Laboratorio-de-audio-del-CMM/IxTL-074/Esquemático/IxTL-074_v.1.0.0.kicad_sch

## KiCad design Esquemático/IxTL-074_v.1.0.0.kicad_sch (2026-10-05)

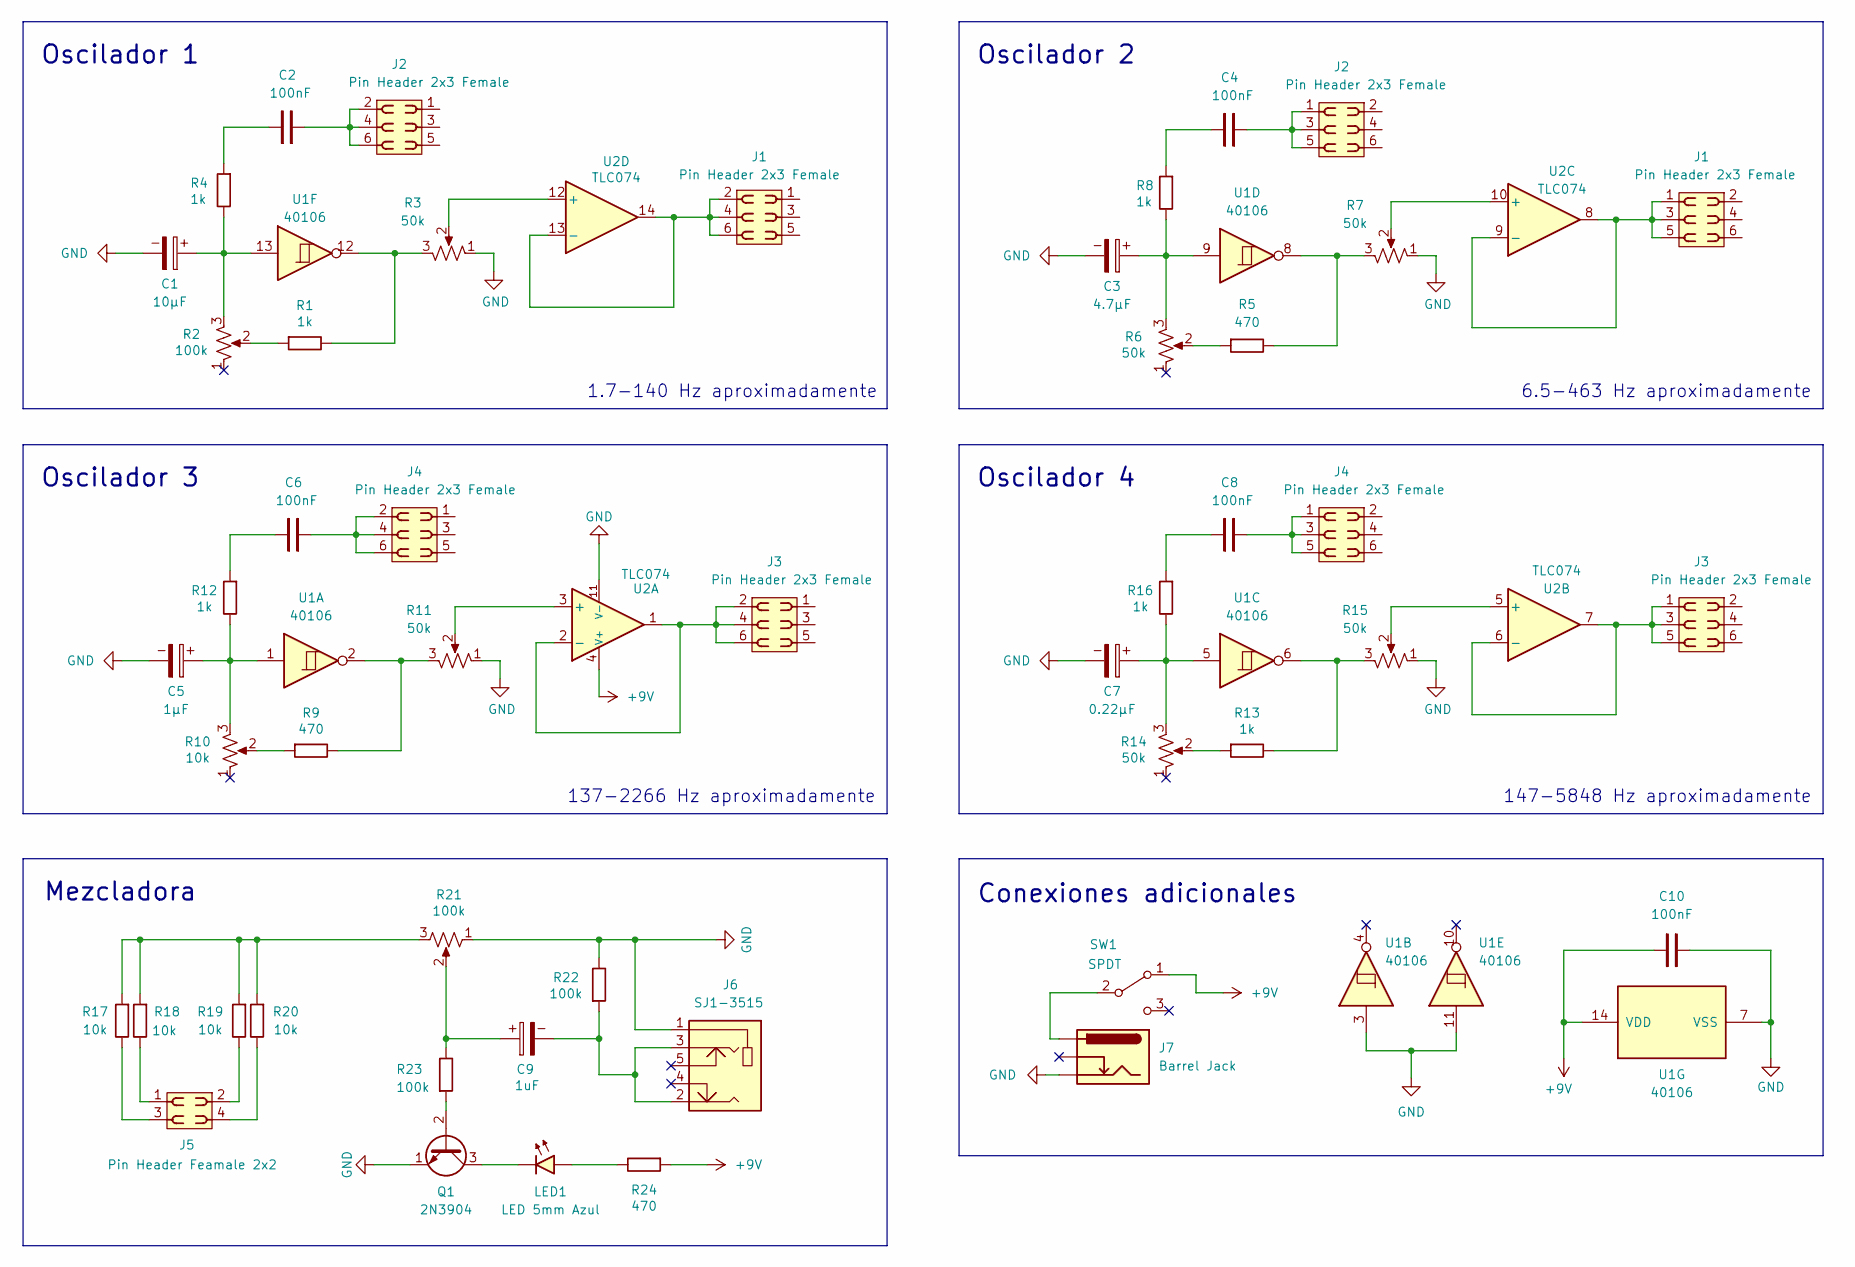
[picture p2: schematic IxTL-074_v.1.0.0.kicad_sch]

Parts:
C1: 10µF; CP_Radial_D5.0mm_P2.00mm
C2, C4, C6, C8, C10: 100nF; C_Disc_D5.0mm_W2.5mm_P2.50mm
C3: 4.7µF; CP_Radial_D5.0mm_P2.00mm
C5: 1µF; CP_Radial_D5.0mm_P2.00mm
C7: 0.22µF; CP_Radial_D5.0mm_P2.00mm
C9: 1uF; CP_Radial_D4.0mm_P1.50mm
J1, J2, J3, J4: Pin Header 2x3 Female; PinSocket_2x03_P2.54mm_Vertical
J5: Pin Header Feamale 2x2; PinSocket_2x02_P2.54mm_Vertical
J6: SJ1-3515; jack-ixtl074
J7: Barrel Jack; Barrel_Jack_PTH_Slot
LED1: LED 5mm Azul; LED_D5.0mm
Q1: 2N3904; TO-92_Inline
R1, R4, R8, R12, R13, R16: 1k; R_Axial_DIN0207_L6.3mm_D2.5mm_P10.16mm_Horizontal
R2, R21: 100k; Bourns-PDB18
R3, R6, R7, R11, R14, R15: 50k; Bourns-PDB18
R5, R9, R24: 470; R_Axial_DIN0207_L6.3mm_D2.5mm_P10.16mm_Horizontal
R10: 10k; Bourns-PDB18
R17, R18, R19, R20: 10k; R_Axial_DIN0207_L6.3mm_D2.5mm_P10.16mm_Horizontal
R22, R23: 100k; R_Axial_DIN0207_L6.3mm_D2.5mm_P10.16mm_Horizontal
SW1: SPDT; Slide_SPDT_PTH_11.6x4.0mm
U1: 40106
U2: TLC074; DIP-14_W7.62mm_LongPads

Connections:
+9V: C10.1, R24.1, SW1.1 (A), U1.14 (VDD), U2.4 (V+)
GND: C1.2, C3.2, C5.2, C7.2, C10.2, J6.1, J7.GND, Q1.1 (E), R3.1, R7.1, R11.1, R15.1, R21.1, R22.2, U1.3, U1.7 (VSS), U1.11, U2.11 (V-)
unnamed: C1.1, R2.3, R4.2, U1.13
unnamed: C2.1, J2.2, J2.4, J2.6
unnamed: C2.2, R4.1
unnamed: C3.1, R6.3, R8.2, U1.9
unnamed: C4.1, J2.1, J2.3, J2.5
unnamed: C4.2, R8.1
unnamed: C5.1, R10.3, R12.2, U1.1
unnamed: C6.1, J4.2, J4.4, J4.6
unnamed: C6.2, R12.1
unnamed: C7.1, R14.3, R16.2, U1.5
unnamed: C8.1, J4.1, J4.3, J4.5
unnamed: C8.2, R16.1
unnamed: C9.1, R21.2, R23.2
unnamed: C9.2, J6.2, J6.3, R22.1
unnamed: J1.1, J1.3, J1.5, U2.8, U2.9 (-)
unnamed: J1.2, J1.4, J1.6, U2.13 (-), U2.14
unnamed: J3.1, J3.3, J3.5, U2.6 (-), U2.7
unnamed: J3.2, J3.4, J3.6, U2.1, U2.2 (-)
unnamed: J5.1, R18.2
unnamed: J5.2, R19.2
unnamed: J5.3, R17.2
unnamed: J5.4, R20.2
unnamed: J7.PWR, SW1.2 (B)
unnamed: LED1.1 (K), Q1.3 (C)
unnamed: LED1.2 (A), R24.2
unnamed: Q1.2 (B), R23.1
unnamed: R1.1, R2.2
unnamed: R1.2, R3.3, U1.12
unnamed: R3.2, U2.12 (+)
unnamed: R5.1, R6.2
unnamed: R5.2, R7.3, U1.8
unnamed: R7.2, U2.10 (+)
unnamed: R9.1, R10.2
unnamed: R11.2, U2.3 (+)
unnamed: R9.2, R11.3, U1.2
unnamed: R13.1, R14.2
unnamed: R13.2, R15.3, U1.6
unnamed: R15.2, U2.5 (+)
unnamed: R17.1, R18.1, R19.1, R20.1, R21.3

Notes on the sheet:
147-5848 Hz aproximadamente
Oscilador 1
1.7-140 Hz aproximadamente
6.5-463 Hz aproximadamente
Oscilador 2
137-2266 Hz aproximadamente
Conexiones adicionales
Oscilador 4
Oscilador 3
Mezcladora
